EosBandi/OSDeluxe/params.cpp

/*
	OSDeluxe - Color PIP Mavlink OSD
	Copyright (C) 2018  Andras Schaffer - Dronedoktor.eu

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
	With Grateful Acknowledgements to the projects:
		AlceOSD by Luis Alves
		PlayUAV OSD
		Brain FPV Flight Controller(https://github.com/BrainFPV/TauLabs) by Tau Labs

 */

#include "osdeluxe.h"

#define PARAM(n, t, p, c) {  n, t, (void *) p,  c }
#define PARAM_END { "" }

int total_params;						// Number of all params (int, to eliminate warning about unsigned, signed comparisions
int param_send_index;

struct param_def parameters[] = {
	//Generic parameters

	PARAM("VIN1_SHARPENING", MAV_PARAM_TYPE_UINT8,&osd.vin_params[0].sharpening, &update_vin_settings),
	PARAM("VIN1_SATURATION", MAV_PARAM_TYPE_UINT8,&osd.vin_params[0].saturation, &update_vin_settings),
	PARAM("VIN1_CONTRAST",   MAV_PARAM_TYPE_UINT8,&osd.vin_params[0].contrast, &update_vin_settings),
	PARAM("VIN1_BRIGHTNESS", MAV_PARAM_TYPE_UINT8,&osd.vin_params[0].brightness, &update_vin_settings),
	PARAM("VIN1_ENHANCE",    MAV_PARAM_TYPE_UINT8,&osd.vin_params[0].enhance, &update_vin_settings),
	PARAM("VIN1_H_MIRROR",   MAV_PARAM_TYPE_UINT8,&osd.vin_params[0].h_mirror, &update_vin_settings),
	PARAM("VIN1_V_MIRROR",   MAV_PARAM_TYPE_UINT8,&osd.vin_params[0].v_mirror, &update_vin_settings),
	PARAM("VIN1_BOUNDARY",   MAV_PARAM_TYPE_UINT8,&osd.vin_params[0].boundary, &update_vin_settings),
	PARAM("VIN1_PEAKING",    MAV_PARAM_TYPE_UINT8,&osd.vin_params[0].peaking, &update_vin_settings),

	PARAM("VIN2_SHARPENING", MAV_PARAM_TYPE_UINT8,&osd.vin_params[1].sharpening, &update_vin_settings),
	PARAM("VIN2_SATURATION", MAV_PARAM_TYPE_UINT8,&osd.vin_params[1].saturation, &update_vin_settings),
	PARAM("VIN2_CONTRAST",   MAV_PARAM_TYPE_UINT8,&osd.vin_params[1].contrast, &update_vin_settings),
	PARAM("VIN2_BRIGHTNESS", MAV_PARAM_TYPE_UINT8,&osd.vin_params[1].brightness, &update_vin_settings),
	PARAM("VIN2_ENHANCE",    MAV_PARAM_TYPE_UINT8,&osd.vin_params[1].enhance, &update_vin_settings),
	PARAM("VIN2_H_MIRROR",   MAV_PARAM_TYPE_UINT8,&osd.vin_params[1].h_mirror, &update_vin_settings),
	PARAM("VIN2_V_MIRROR",   MAV_PARAM_TYPE_UINT8,&osd.vin_params[1].v_mirror, &update_vin_settings),
	PARAM("VIN2_BOUNDARY",   MAV_PARAM_TYPE_UINT8,&osd.vin_params[1].boundary, &update_vin_settings),
	PARAM("VIN2_PEAKING",    MAV_PARAM_TYPE_UINT8,&osd.vin_params[1].peaking, &update_vin_settings),

	PARAM("VIN3_SHARPENING", MAV_PARAM_TYPE_UINT8,&osd.vin_params[2].sharpening, &update_vin_settings),
	PARAM("VIN3_SATURATION", MAV_PARAM_TYPE_UINT8,&osd.vin_params[2].saturation, &update_vin_settings),
	PARAM("VIN3_CONTRAST",   MAV_PARAM_TYPE_UINT8,&osd.vin_params[2].contrast, &update_vin_settings),
	PARAM("VIN3_BRIGHTNESS", MAV_PARAM_TYPE_UINT8,&osd.vin_params[2].brightness, &update_vin_settings),
	PARAM("VIN3_ENHANCE",    MAV_PARAM_TYPE_UINT8,&osd.vin_params[2].enhance, &update_vin_settings),
	PARAM("VIN3_H_MIRROR",   MAV_PARAM_TYPE_UINT8,&osd.vin_params[2].h_mirror, &update_vin_settings),
	PARAM("VIN3_V_MIRROR",   MAV_PARAM_TYPE_UINT8,&osd.vin_params[2].v_mirror, &update_vin_settings),
	PARAM("VIN3_BOUNDARY",   MAV_PARAM_TYPE_UINT8,&osd.vin_params[2].boundary, &update_vin_settings),
	PARAM("VIN3_PEAKING",    MAV_PARAM_TYPE_UINT8,&osd.vin_params[2].peaking, &update_vin_settings),

	PARAM("VIN4_SHARPENING", MAV_PARAM_TYPE_UINT8,&osd.vin_params[3].sharpening, &update_vin_settings),
	PARAM("VIN4_SATURATION", MAV_PARAM_TYPE_UINT8,&osd.vin_params[3].saturation, &update_vin_settings),
	PARAM("VIN4_CONTRAST",   MAV_PARAM_TYPE_UINT8,&osd.vin_params[3].contrast, &update_vin_settings),
	PARAM("VIN4_BRIGHTNESS", MAV_PARAM_TYPE_UINT8,&osd.vin_params[3].brightness, &update_vin_settings),
	PARAM("VIN4_ENHANCE",    MAV_PARAM_TYPE_UINT8,&osd.vin_params[3].enhance, &update_vin_settings),
	PARAM("VIN4_H_MIRROR",   MAV_PARAM_TYPE_UINT8,&osd.vin_params[3].h_mirror, &update_vin_settings),
	PARAM("VIN4_V_MIRROR",   MAV_PARAM_TYPE_UINT8,&osd.vin_params[3].v_mirror, &update_vin_settings),
	PARAM("VIN4_BOUNDARY",   MAV_PARAM_TYPE_UINT8,&osd.vin_params[3].boundary, &update_vin_settings),
	PARAM("VIN4_PEAKING",    MAV_PARAM_TYPE_UINT8,&osd.vin_params[3].peaking, &update_vin_settings),


	PARAM("VARIO_POSX", MAV_PARAM_TYPE_UINT16, &osd.vario.x, NULL),
	PARAM("VARIO_POSY", MAV_PARAM_TYPE_UINT16, &osd.vario.y, NULL),
	PARAM("VARIO_HEIGHT", MAV_PARAM_TYPE_UINT16, &osd.vario.h, NULL),
	PARAM("VARIO_WIDTH", MAV_PARAM_TYPE_UINT16, &osd.vario.w, NULL),
	PARAM("VARIO_NUMPOS", MAV_PARAM_TYPE_UINT8, &osd.vario.num_pos, NULL),
	PARAM("VARIO_MAXIMUM", MAV_PARAM_TYPE_REAL32, &osd.vario.vario_max, NULL),

	PARAM("VGRAPH_POSX", MAV_PARAM_TYPE_UINT16, &osd.vgraph.x, &do_update_pthy),
	PARAM("VGRAPH_POSY", MAV_PARAM_TYPE_UINT16, &osd.vgraph.y, &do_update_pthy),
	PARAM("VGRAPH_HEIGHT", MAV_PARAM_TYPE_UINT16, &osd.vgraph.h, &do_update_pthy),
	PARAM("VGRAPH_MAXIMUM", MAV_PARAM_TYPE_REAL32, &osd.vgraph.vario_max, NULL),
	PARAM("VGRAPH_MIX", MAV_PARAM_TYPE_UINT8, &osd.vgraph.mix, NULL),


	PARAM("GPS_POSX", MAV_PARAM_TYPE_UINT16, &osd.gps.x, NULL),
	PARAM("GPS_POSY", MAV_PARAM_TYPE_UINT16, &osd.gps.y, NULL),
	PARAM("GPS_SAT_WARNING", MAV_PARAM_TYPE_UINT8, &osd.gps.sat_warn, NULL),
	PARAM("GPS_HDOP_WARNING", MAV_PARAM_TYPE_REAL32, &osd.gps.hdop_warn, NULL),
	PARAM("GPS_SAT_CRITICAL", MAV_PARAM_TYPE_UINT8, &osd.gps.sat_critical, NULL),
	PARAM("GPS_HDOP_CRITCAL", MAV_PARAM_TYPE_REAL32, &osd.gps.hdop_critical, NULL),

	PARAM("RSSI_POSX", MAV_PARAM_TYPE_UINT16, &osd.rssi.x, NULL),
	PARAM("RSSI_POSY", MAV_PARAM_TYPE_UINT16, &osd.rssi.y, NULL),
	PARAM("RSSI_WARNING", MAV_PARAM_TYPE_UINT8, &osd.rssi.rssi_warning, NULL),
	PARAM("RSSI_CRITICAL", MAV_PARAM_TYPE_UINT8, &osd.rssi.rssi_critical, NULL),


//     01234567890123456
	PARAM("BAT1V_POSX", MAV_PARAM_TYPE_UINT16, &osd.batt1_v.x, NULL),
	PARAM("BAT1V_POSY", MAV_PARAM_TYPE_UINT16, &osd.batt1_v.y, NULL),
	PARAM("BAT1V_CELLS", MAV_PARAM_TYPE_UINT8, &osd.batt1_v.cells, NULL),
	PARAM("BAT1V_MINCELLV", MAV_PARAM_TYPE_REAL32, &osd.batt1_v.min_cell_voltage, NULL),
	PARAM("BAT1V_MAXCELLV", MAV_PARAM_TYPE_REAL32, &osd.batt1_v.max_cell_voltage, NULL),
	PARAM("BAT1V_YELWCELLV", MAV_PARAM_TYPE_REAL32, &osd.batt1_v.yellow_cell_voltage, NULL),
	PARAM("BAT1V_REDCELLV", MAV_PARAM_TYPE_REAL32, &osd.batt1_v.red_cell_voltage, NULL),
	PARAM("BAT1V_BARTYPE", MAV_PARAM_TYPE_UINT8, &osd.batt1_v.bar_type, NULL),

	PARAM("BAT2V_POSX", MAV_PARAM_TYPE_UINT16, &osd.batt2_v.x, NULL),
	PARAM("BAT2V_POSY", MAV_PARAM_TYPE_UINT16, &osd.batt2_v.y, NULL),
	PARAM("BAT2V_CELLS", MAV_PARAM_TYPE_UINT8, &osd.batt2_v.cells, NULL),
	PARAM("BAT2V_MINCELLV", MAV_PARAM_TYPE_REAL32, &osd.batt2_v.min_cell_voltage, NULL),
	PARAM("BAT2V_MAXCELLV", MAV_PARAM_TYPE_REAL32, &osd.batt2_v.max_cell_voltage, NULL),
	PARAM("BAT2V_YELWCELLV", MAV_PARAM_TYPE_REAL32, &osd.batt2_v.yellow_cell_voltage, NULL),
	PARAM("BAT2V_REDCELLV", MAV_PARAM_TYPE_REAL32, &osd.batt2_v.red_cell_voltage, NULL),
	PARAM("BAT2V_BARTYPE", MAV_PARAM_TYPE_UINT8, &osd.batt2_v.bar_type, NULL),

	PARAM("BAT1CAP_POSX", MAV_PARAM_TYPE_UINT16, &osd.batt1_cap.x, NULL),
	PARAM("BAT1CAP_POSY", MAV_PARAM_TYPE_UINT16, &osd.batt1_cap.y, NULL),
	PARAM("BAT1CAP_BARTYPE", MAV_PARAM_TYPE_UINT8, &osd.batt1_cap.bar_type, NULL),

	PARAM("BAT1CUR_POSX", MAV_PARAM_TYPE_UINT16, &osd.batt1_curr.x, NULL),
	PARAM("BAT1CUR_POSY", MAV_PARAM_TYPE_UINT16, &osd.batt1_curr.y, NULL),

	PARAM("BAT2CUR_POSX", MAV_PARAM_TYPE_UINT16, &osd.batt2_curr.x, NULL),
	PARAM("BAT2CUR_POSY", MAV_PARAM_TYPE_UINT16, &osd.batt2_curr.y, NULL),

	PARAM("BAT1PWR_POSX", MAV_PARAM_TYPE_UINT16, &osd.batt1_power.x, NULL),
	PARAM("BAT1PWR_POSY", MAV_PARAM_TYPE_UINT16, &osd.batt1_power.y, NULL),

	PARAM("BAT2PWR_POSX", MAV_PARAM_TYPE_UINT16, &osd.batt2_power.x, NULL),
	PARAM("BAT2PWR_POSY", MAV_PARAM_TYPE_UINT16, &osd.batt2_power.y, NULL),

	PARAM("STATUS_POSX", MAV_PARAM_TYPE_UINT16, &osd.stat.x, NULL),
	PARAM("STATUS_POSY", MAV_PARAM_TYPE_UINT16, &osd.stat.y, NULL),

	PARAM("ALT_POSX", MAV_PARAM_TYPE_UINT16, &osd.alt.x, NULL),
	PARAM("ALT_POSY", MAV_PARAM_TYPE_UINT16, &osd.alt.y, NULL),

	PARAM("COMPASS_POSX", MAV_PARAM_TYPE_UINT16, &osd.compass.x, NULL),
	PARAM("COMPASS_POSY", MAV_PARAM_TYPE_UINT16, &osd.compass.y, NULL),

	PARAM("PULL_POSX", MAV_PARAM_TYPE_UINT16, &osd.pull.x, NULL),
	PARAM("PULL_POSY", MAV_PARAM_TYPE_UINT16, &osd.pull.y, NULL),
	PARAM("PULL_WARNING", MAV_PARAM_TYPE_REAL32, &osd.pull.warning, NULL),

	PARAM("HOME_POSX", MAV_PARAM_TYPE_UINT16, &osd.home_w.x, NULL),
	PARAM("HOME_POSY", MAV_PARAM_TYPE_UINT16, &osd.home_w.y, NULL),

	PARAM("MODE_POSX", MAV_PARAM_TYPE_UINT16, &osd.mode.mode_x, NULL),
	PARAM("MODE_POSY", MAV_PARAM_TYPE_UINT16, &osd.mode.mode_y, NULL),
	PARAM("MODE_CENTERED", MAV_PARAM_TYPE_UINT8, &osd.mode.mode_centered, NULL),
	PARAM("MODE_SHORT", MAV_PARAM_TYPE_UINT8, &osd.mode.mode_short, NULL),

	PARAM("FAILSAFE_POSX", MAV_PARAM_TYPE_UINT16, &osd.mode.fs_x, NULL),
	PARAM("FAILSAFE_POSY", MAV_PARAM_TYPE_UINT16, &osd.mode.fs_y, NULL),
	PARAM("FAILSAFE_CENTERD", MAV_PARAM_TYPE_UINT8, &osd.mode.fs_centered, NULL),

	PARAM("ARM_POSX", MAV_PARAM_TYPE_UINT16, &osd.mode.arm_x, NULL),
	PARAM("ARM_POSY", MAV_PARAM_TYPE_UINT16, &osd.mode.arm_y, NULL),
	PARAM("ARM_CENTERD", MAV_PARAM_TYPE_UINT8, &osd.mode.arm_centered, NULL),

	PARAM("MESSAGE_POSX", MAV_PARAM_TYPE_UINT16, &osd.msg_widget.x, NULL),
	PARAM("MESSAGE_POSY", MAV_PARAM_TYPE_UINT16, &osd.msg_widget.y, NULL),

	PARAM("MSG_LIST_POSX", MAV_PARAM_TYPE_UINT16, &osd.msg_list_widget.x, NULL), 
	PARAM("MSG_LIST_POSY", MAV_PARAM_TYPE_UINT16, &osd.msg_list_widget.y, NULL),


	PARAM("GS_POSX", MAV_PARAM_TYPE_UINT16, &osd.gs.x, NULL),
	PARAM("GS_POSY", MAV_PARAM_TYPE_UINT16, &osd.gs.y, NULL),

	PARAM("THROTTLE_POSX", MAV_PARAM_TYPE_UINT16, &osd.thr.x, NULL),
	PARAM("THROTTLE_POSY", MAV_PARAM_TYPE_UINT16, &osd.thr.y, NULL),

	PARAM("MOVE_POSX", MAV_PARAM_TYPE_UINT16, &osd.move.x, &do_update_pthy),
	PARAM("MOVE_POSY", MAV_PARAM_TYPE_UINT16, &osd.move.y, &do_update_pthy),
	PARAM("MOVE_SIZE", MAV_PARAM_TYPE_UINT16, &osd.move.size, &do_update_pthy),
	PARAM("MOVE_MAX",  MAV_PARAM_TYPE_REAL32, &osd.move.max, NULL),

	PARAM("RADAR1_POSX", MAV_PARAM_TYPE_UINT16, &osd.radar1.x, &do_update_pthy),
	PARAM("RADAR1_POSY", MAV_PARAM_TYPE_UINT16, &osd.radar1.y, &do_update_pthy),
	PARAM("RADAR1_SIZE", MAV_PARAM_TYPE_UINT16, &osd.radar1.size, &do_update_pthy),
	PARAM("RADAR1_SCALE", MAV_PARAM_TYPE_UINT8, &osd.radar1.scale, &do_update_pthy),
	PARAM("RADAR1_TYPE", MAV_PARAM_TYPE_UINT8, &osd.radar1.type, &do_update_pthy),

	PARAM("RADAR2_POSX", MAV_PARAM_TYPE_UINT16, &osd.radar2.x, &do_update_pthy),
	PARAM("RADAR2_POSY", MAV_PARAM_TYPE_UINT16, &osd.radar2.y, &do_update_pthy),
	PARAM("RADAR2_SIZE", MAV_PARAM_TYPE_UINT16, &osd.radar2.size, &do_update_pthy),
	PARAM("RADAR2_SCALE", MAV_PARAM_TYPE_UINT8, &osd.radar2.scale, &do_update_pthy),
	PARAM("RADAR2_TYPE", MAV_PARAM_TYPE_UINT8, &osd.radar2.type, &do_update_pthy),

	PARAM("RADAR3_POSX", MAV_PARAM_TYPE_UINT16, &osd.radar3.x, &do_update_pthy),
	PARAM("RADAR3_POSY", MAV_PARAM_TYPE_UINT16, &osd.radar3.y, &do_update_pthy),
	PARAM("RADAR3_SIZE", MAV_PARAM_TYPE_UINT16, &osd.radar3.size, &do_update_pthy),
	PARAM("RADAR3_SCALE", MAV_PARAM_TYPE_UINT8, &osd.radar3.scale, &do_update_pthy),
	PARAM("RADAR3_TYPE", MAV_PARAM_TYPE_UINT8, &osd.radar3.type, &do_update_pthy),

	PARAM("CTR_RC_CH_1", MAV_PARAM_TYPE_UINT8, &osd.ctr_ch[0], NULL),
	PARAM("CTR_RC_CH_2", MAV_PARAM_TYPE_UINT8, &osd.ctr_ch[1], NULL),
	PARAM("CTR_RC_CH_3", MAV_PARAM_TYPE_UINT8, &osd.ctr_ch[2], NULL),
	PARAM("CTR_RC_CH_4", MAV_PARAM_TYPE_UINT8, &osd.ctr_ch[3], NULL),

	//bit coded field for osd widget visibility by pages (1-8 pages)
	PARAM("PAGE_GPS", MAV_PARAM_TYPE_UINT8, &osd.gps.visible, NULL),
	PARAM("PAGE_BATT1_VOLT", MAV_PARAM_TYPE_UINT8, &osd.batt1_v.visible, NULL),
	PARAM("PAGE_BATT2_VOLT", MAV_PARAM_TYPE_UINT8, &osd.batt2_v.visible, NULL),
	PARAM("PAGE_BATT1_CURR", MAV_PARAM_TYPE_UINT8, &osd.batt1_curr.visible, NULL),
	PARAM("PAGE_BATT2_CURR", MAV_PARAM_TYPE_UINT8, &osd.batt2_curr.visible, NULL),
	PARAM("PAGE_BATT1_CAP", MAV_PARAM_TYPE_UINT8, &osd.batt1_cap.visible, NULL),
	PARAM("PAGE_BATT1_PWR", MAV_PARAM_TYPE_UINT8, &osd.batt1_power.visible, NULL),
	PARAM("PAGE_BATT2_PWR", MAV_PARAM_TYPE_UINT8, &osd.batt2_power.visible, NULL),

	PARAM("PAGE_STAT", MAV_PARAM_TYPE_UINT8, &osd.stat.visible, NULL),
	PARAM("PAGE_ALT", MAV_PARAM_TYPE_UINT8, &osd.alt.visible, NULL),
	PARAM("PAGE_COMPASS", MAV_PARAM_TYPE_UINT8, &osd.compass.visible, NULL),
	PARAM("PAGE_VARIO", MAV_PARAM_TYPE_UINT8, &osd.vario.visible, NULL),
	PARAM("PAGE_HOME", MAV_PARAM_TYPE_UINT8, &osd.home_w.visible, NULL),
	PARAM("PAGE_HORIZON", MAV_PARAM_TYPE_UINT8, &osd.horizon.visible, NULL),
	PARAM("PAGE_MODE", MAV_PARAM_TYPE_UINT8, &osd.mode.visible, NULL),
	PARAM("PAGE_PULL", MAV_PARAM_TYPE_UINT8, &osd.pull.visible, NULL),
	PARAM("PAGE_MESSAGE", MAV_PARAM_TYPE_UINT8, &osd.msg_widget.visible, NULL),
	PARAM("PAGE_GS", MAV_PARAM_TYPE_UINT8, &osd.gs.visible, NULL),
	PARAM("PAGE_THROTTLE", MAV_PARAM_TYPE_UINT8, &osd.thr.visible, NULL),
    PARAM("PAGE_MOVE", MAV_PARAM_TYPE_UINT8, &osd.move.visible, NULL), 
	PARAM("PAGE_PT", MAV_PARAM_TYPE_UINT8, &osd.pt_widget.visible, NULL),
	PARAM("PAGE_CENTER_M", MAV_PARAM_TYPE_UINT8, &osd.center_cross_visible , &do_update_pthy),
	PARAM("PAGE_RADAR1", MAV_PARAM_TYPE_UINT8, &osd.radar1.visible, &do_update_pthy),
	PARAM("PAGE_RADAR2", MAV_PARAM_TYPE_UINT8, &osd.radar2.visible, &do_update_pthy),
	PARAM("PAGE_RADAR3", MAV_PARAM_TYPE_UINT8, &osd.radar3.visible, &do_update_pthy),
    PARAM("PAGE_RSSI",MAV_PARAM_TYPE_UINT8, &osd.rssi.visible, &do_update_pthy),
	PARAM("PAGE_EKF", MAV_PARAM_TYPE_UINT8, &osd.ekf_detail.visible, NULL), 
	PARAM("PAGE_VIBE", MAV_PARAM_TYPE_UINT8, &osd.vibe_detail.visible, NULL),
	PARAM("PAGE_MSG_LIST", MAV_PARAM_TYPE_UINT8, &osd.msg_list_widget.visible, NULL), 
	PARAM("PAGE_RCOUT", MAV_PARAM_TYPE_UINT8, &osd.rc_out.visible, NULL),


		
	PARAM("PAGE_BOX_1", MAV_PARAM_TYPE_INT16, &osd.boxes[0].visible, &do_update_pthy),
	PARAM("PAGE_BOX_2", MAV_PARAM_TYPE_INT16, &osd.boxes[1].visible, &do_update_pthy),
	PARAM("PAGE_BOX_3", MAV_PARAM_TYPE_INT16, &osd.boxes[2].visible, &do_update_pthy),
	PARAM("PAGE_BOX_4", MAV_PARAM_TYPE_INT16, &osd.boxes[3].visible, &do_update_pthy),
	PARAM("PAGE_BOX_5", MAV_PARAM_TYPE_INT16, &osd.boxes[4].visible, &do_update_pthy),
	PARAM("PAGE_BOX_6", MAV_PARAM_TYPE_INT16, &osd.boxes[5].visible, &do_update_pthy),
	PARAM("PAGE_BOX_7", MAV_PARAM_TYPE_INT16, &osd.boxes[6].visible, &do_update_pthy),
	PARAM("PAGE_BOX_8", MAV_PARAM_TYPE_INT16, &osd.boxes[7].visible, &do_update_pthy),

	PARAM("VOUT_COLOR_BAR", MAV_PARAM_TYPE_UINT8, &osd.color_bar_x, &update_vout_settings),
	PARAM("VOUT_COLOR_KILL", MAV_PARAM_TYPE_UINT8, &osd.color_kill_x, &update_vout_settings),
	PARAM("VOUT_OUT1_GAIN", MAV_PARAM_TYPE_UINT8, &osd.vout1_gain, &update_vout_settings),
	PARAM("VOUT_OUT2_GAIN", MAV_PARAM_TYPE_UINT8, &osd.vout2_gain, &update_vout_settings),
	PARAM("VOUT_OUT3_GAIN", MAV_PARAM_TYPE_UINT8, &osd.vout3_gain, &update_vout_settings),


	PARAM("PIPM0_POS_H_CH1", MAV_PARAM_TYPE_UINT8, &osd.video_channels[0][1].pos_h, &update_pip),
	PARAM("PIPM0_POS_V_CH1", MAV_PARAM_TYPE_UINT8, &osd.video_channels[0][1].pos_v, &update_pip),
	PARAM("PIPM0_SIZE_CH1",  MAV_PARAM_TYPE_UINT8, &osd.video_channels[0][1].len_h, &update_pip),
	PARAM("PIPM0_INPUT_CH1", MAV_PARAM_TYPE_UINT8, &osd.video_channels[0][1].input, &update_pip),
	PARAM("PIPM0_POPUP_CH1", MAV_PARAM_TYPE_UINT8, &osd.video_channels[0][1].popup, &update_pip),
	PARAM("PIPM0_ENA_CH1",   MAV_PARAM_TYPE_UINT8, &osd.video_channels[0][1].enable, &update_pip),

	PARAM("PIPM0_POS_H_CH2", MAV_PARAM_TYPE_UINT8, &osd.video_channels[0][2].pos_h, &update_pip),
	PARAM("PIPM0_POS_V_CH2", MAV_PARAM_TYPE_UINT8, &osd.video_channels[0][2].pos_v, &update_pip),
	PARAM("PIPM0_SIZE_CH2",  MAV_PARAM_TYPE_UINT8, &osd.video_channels[0][2].len_h, &update_pip),
	PARAM("PIPM0_INPUT_CH2", MAV_PARAM_TYPE_UINT8, &osd.video_channels[0][2].input, &update_pip),
	PARAM("PIPM0_POPUP_CH2", MAV_PARAM_TYPE_UINT8, &osd.video_channels[0][2].popup, &update_pip),
	PARAM("PIPM0_ENA_CH2",   MAV_PARAM_TYPE_UINT8, &osd.video_channels[0][2].enable, &update_pip),

	PARAM("PIPM0_POS_H_CH3", MAV_PARAM_TYPE_UINT8, &osd.video_channels[0][3].pos_h, &update_pip),
	PARAM("PIPM0_POS_V_CH3", MAV_PARAM_TYPE_UINT8, &osd.video_channels[0][3].pos_v, &update_pip),
	PARAM("PIPM0_SIZE_CH3",  MAV_PARAM_TYPE_UINT8, &osd.video_channels[0][3].len_h, &update_pip),
	PARAM("PIPM0_INPUT_CH3", MAV_PARAM_TYPE_UINT8, &osd.video_channels[0][3].input, &update_pip),
	PARAM("PIPM0_POPUP_CH3", MAV_PARAM_TYPE_UINT8, &osd.video_channels[0][3].popup, &update_pip),
	PARAM("PIPM0_ENA_CH3",   MAV_PARAM_TYPE_UINT8, &osd.video_channels[0][3].enable, &update_pip),

	PARAM("PIPM0_POS_H_CH4", MAV_PARAM_TYPE_UINT8, &osd.video_channels[0][4].pos_h, &update_pip),
	PARAM("PIPM0_POS_V_CH4", MAV_PARAM_TYPE_UINT8, &osd.video_channels[0][4].pos_v, &update_pip),
	PARAM("PIPM0_SIZE_CH4",  MAV_PARAM_TYPE_UINT8, &osd.video_channels[0][4].len_h, &update_pip),
	PARAM("PIPM0_INPUT_CH4", MAV_PARAM_TYPE_UINT8, &osd.video_channels[0][4].input, &update_pip),
	PARAM("PIPM0_POPUP_CH4", MAV_PARAM_TYPE_UINT8, &osd.video_channels[0][4].popup, &update_pip),
	PARAM("PIPM0_ENA_CH4",   MAV_PARAM_TYPE_UINT8, &osd.video_channels[0][4].enable, &update_pip),

	PARAM("PIPM1_POS_H_CH1", MAV_PARAM_TYPE_UINT8, &osd.video_channels[1][1].pos_h, &update_pip),
	PARAM("PIPM1_POS_V_CH1", MAV_PARAM_TYPE_UINT8, &osd.video_channels[1][1].pos_v, &update_pip),
	PARAM("PIPM1_SIZE_CH1",  MAV_PARAM_TYPE_UINT8, &osd.video_channels[1][1].len_h, &update_pip),
	PARAM("PIPM1_INPUT_CH1", MAV_PARAM_TYPE_UINT8, &osd.video_channels[1][1].input, &update_pip),
	PARAM("PIPM1_POPUP_CH1", MAV_PARAM_TYPE_UINT8, &osd.video_channels[1][1].popup, &update_pip),
	PARAM("PIPM1_ENA_CH1",   MAV_PARAM_TYPE_UINT8, &osd.video_channels[1][1].enable, &update_pip),

	PARAM("PIPM1_POS_H_CH2", MAV_PARAM_TYPE_UINT8, &osd.video_channels[1][2].pos_h, &update_pip),
	PARAM("PIPM1_POS_V_CH2", MAV_PARAM_TYPE_UINT8, &osd.video_channels[1][2].pos_v, &update_pip),
	PARAM("PIPM1_SIZE_CH2",  MAV_PARAM_TYPE_UINT8, &osd.video_channels[1][2].len_h, &update_pip),
	PARAM("PIPM1_INPUT_CH2", MAV_PARAM_TYPE_UINT8, &osd.video_channels[1][2].input, &update_pip),
	PARAM("PIPM1_POPUP_CH2", MAV_PARAM_TYPE_UINT8, &osd.video_channels[1][2].popup, &update_pip),
	PARAM("PIPM1_ENA_CH2",   MAV_PARAM_TYPE_UINT8, &osd.video_channels[1][2].enable, &update_pip),

	PARAM("PIPM1_POS_H_CH3", MAV_PARAM_TYPE_UINT8, &osd.video_channels[1][3].pos_h, &update_pip),
	PARAM("PIPM1_POS_V_CH3", MAV_PARAM_TYPE_UINT8, &osd.video_channels[1][3].pos_v, &update_pip),
	PARAM("PIPM1_SIZE_CH3",  MAV_PARAM_TYPE_UINT8, &osd.video_channels[1][3].len_h, &update_pip),
	PARAM("PIPM1_INPUT_CH3", MAV_PARAM_TYPE_UINT8, &osd.video_channels[1][3].input, &update_pip),
	PARAM("PIPM1_POPUP_CH3", MAV_PARAM_TYPE_UINT8, &osd.video_channels[1][3].popup, &update_pip),
	PARAM("PIPM1_ENA_CH3",   MAV_PARAM_TYPE_UINT8, &osd.video_channels[1][3].enable, &update_pip),

	PARAM("PIPM1_POS_H_CH4", MAV_PARAM_TYPE_UINT8, &osd.video_channels[1][4].pos_h, &update_pip),
	PARAM("PIPM1_POS_V_CH4", MAV_PARAM_TYPE_UINT8, &osd.video_channels[1][4].pos_v, &update_pip),
	PARAM("PIPM1_SIZE_CH4",  MAV_PARAM_TYPE_UINT8, &osd.video_channels[1][4].len_h, &update_pip),
	PARAM("PIPM1_INPUT_CH4", MAV_PARAM_TYPE_UINT8, &osd.video_channels[1][4].input, &update_pip),
	PARAM("PIPM1_POPUP_CH4", MAV_PARAM_TYPE_UINT8, &osd.video_channels[1][4].popup, &update_pip),
	PARAM("PIPM1_ENA_CH4",   MAV_PARAM_TYPE_UINT8, &osd.video_channels[1][4].enable, &update_pip),
//---
	PARAM("PIPM2_POS_H_CH1", MAV_PARAM_TYPE_UINT8, &osd.video_channels[2][1].pos_h, &update_pip),
	PARAM("PIPM2_POS_V_CH1", MAV_PARAM_TYPE_UINT8, &osd.video_channels[2][1].pos_v, &update_pip),
	PARAM("PIPM2_SIZE_CH1",  MAV_PARAM_TYPE_UINT8, &osd.video_channels[2][1].len_h, &update_pip),
	PARAM("PIPM2_INPUT_CH1", MAV_PARAM_TYPE_UINT8, &osd.video_channels[2][1].input, &update_pip),
	PARAM("PIPM2_POPUP_CH1", MAV_PARAM_TYPE_UINT8, &osd.video_channels[2][1].popup, &update_pip),
	PARAM("PIPM2_ENA_CH1",   MAV_PARAM_TYPE_UINT8, &osd.video_channels[2][1].enable, &update_pip),

	PARAM("PIPM2_POS_H_CH2", MAV_PARAM_TYPE_UINT8, &osd.video_channels[2][2].pos_h, &update_pip),
	PARAM("PIPM2_POS_V_CH2", MAV_PARAM_TYPE_UINT8, &osd.video_channels[2][2].pos_v, &update_pip),
	PARAM("PIPM2_SIZE_CH2",  MAV_PARAM_TYPE_UINT8, &osd.video_channels[2][2].len_h, &update_pip),
	PARAM("PIPM2_INPUT_CH2", MAV_PARAM_TYPE_UINT8, &osd.video_channels[2][2].input, &update_pip),
	PARAM("PIPM2_POPUP_CH2", MAV_PARAM_TYPE_UINT8, &osd.video_channels[2][2].popup, &update_pip),
	PARAM("PIPM2_ENA_CH2",   MAV_PARAM_TYPE_UINT8, &osd.video_channels[2][2].enable, &update_pip),

	PARAM("PIPM2_POS_H_CH3", MAV_PARAM_TYPE_UINT8, &osd.video_channels[2][3].pos_h, &update_pip),
	PARAM("PIPM2_POS_V_CH3", MAV_PARAM_TYPE_UINT8, &osd.video_channels[2][3].pos_v, &update_pip),
	PARAM("PIPM2_SIZE_CH3",  MAV_PARAM_TYPE_UINT8, &osd.video_channels[2][3].len_h, &update_pip),
	PARAM("PIPM2_INPUT_CH3", MAV_PARAM_TYPE_UINT8, &osd.video_channels[2][3].input, &update_pip),
	PARAM("PIPM2_POPUP_CH3", MAV_PARAM_TYPE_UINT8, &osd.video_channels[2][3].popup, &update_pip),
	PARAM("PIPM2_ENA_CH3",   MAV_PARAM_TYPE_UINT8, &osd.video_channels[2][3].enable, &update_pip),

	PARAM("PIPM2_POS_H_CH4", MAV_PARAM_TYPE_UINT8, &osd.video_channels[2][4].pos_h, &update_pip),
	PARAM("PIPM2_POS_V_CH4", MAV_PARAM_TYPE_UINT8, &osd.video_channels[2][4].pos_v, &update_pip),
	PARAM("PIPM2_SIZE_CH4",  MAV_PARAM_TYPE_UINT8, &osd.video_channels[2][4].len_h, &update_pip),
	PARAM("PIPM2_INPUT_CH4", MAV_PARAM_TYPE_UINT8, &osd.video_channels[2][4].input, &update_pip),
	PARAM("PIPM2_POPUP_CH4", MAV_PARAM_TYPE_UINT8, &osd.video_channels[2][4].popup, &update_pip),
	PARAM("PIPM2_ENA_CH4",   MAV_PARAM_TYPE_UINT8, &osd.video_channels[2][4].enable, &update_pip),
//---
	PARAM("PIPM3_POS_H_CH1", MAV_PARAM_TYPE_UINT8, &osd.video_channels[3][1].pos_h, &update_pip),
	PARAM("PIPM3_POS_V_CH1", MAV_PARAM_TYPE_UINT8, &osd.video_channels[3][1].pos_v, &update_pip),
	PARAM("PIPM3_SIZE_CH1",  MAV_PARAM_TYPE_UINT8, &osd.video_channels[3][1].len_h, &update_pip),
	PARAM("PIPM3_INPUT_CH1", MAV_PARAM_TYPE_UINT8, &osd.video_channels[3][1].input, &update_pip),
	PARAM("PIPM3_POPUP_CH1", MAV_PARAM_TYPE_UINT8, &osd.video_channels[3][1].popup, &update_pip),
	PARAM("PIPM3_ENA_CH1",   MAV_PARAM_TYPE_UINT8, &osd.video_channels[3][1].enable, &update_pip),

	PARAM("PIPM3_POS_H_CH2", MAV_PARAM_TYPE_UINT8, &osd.video_channels[3][2].pos_h, &update_pip),
	PARAM("PIPM3_POS_V_CH2", MAV_PARAM_TYPE_UINT8, &osd.video_channels[3][2].pos_v, &update_pip),
	PARAM("PIPM3_SIZE_CH2",  MAV_PARAM_TYPE_UINT8, &osd.video_channels[3][2].len_h, &update_pip),
	PARAM("PIPM3_INPUT_CH2", MAV_PARAM_TYPE_UINT8, &osd.video_channels[3][2].input, &update_pip),
	PARAM("PIPM3_POPUP_CH2", MAV_PARAM_TYPE_UINT8, &osd.video_channels[3][2].popup, &update_pip),
	PARAM("PIPM3_ENA_CH2",   MAV_PARAM_TYPE_UINT8, &osd.video_channels[3][2].enable, &update_pip),

	PARAM("PIPM3_POS_H_CH3", MAV_PARAM_TYPE_UINT8, &osd.video_channels[3][3].pos_h, &update_pip),
	PARAM("PIPM3_POS_V_CH3", MAV_PARAM_TYPE_UINT8, &osd.video_channels[3][3].pos_v, &update_pip),
	PARAM("PIPM3_SIZE_CH3",  MAV_PARAM_TYPE_UINT8, &osd.video_channels[3][3].len_h, &update_pip),
	PARAM("PIPM3_INPUT_CH3", MAV_PARAM_TYPE_UINT8, &osd.video_channels[3][3].input, &update_pip),
	PARAM("PIPM3_POPUP_CH3", MAV_PARAM_TYPE_UINT8, &osd.video_channels[3][3].popup, &update_pip),
	PARAM("PIPM3_ENA_CH3",   MAV_PARAM_TYPE_UINT8, &osd.video_channels[3][3].enable, &update_pip),

	PARAM("PIPM3_POS_H_CH4", MAV_PARAM_TYPE_UINT8, &osd.video_channels[3][4].pos_h, &update_pip),
	PARAM("PIPM3_POS_V_CH4", MAV_PARAM_TYPE_UINT8, &osd.video_channels[3][4].pos_v, &update_pip),
	PARAM("PIPM3_SIZE_CH4",  MAV_PARAM_TYPE_UINT8, &osd.video_channels[3][4].len_h, &update_pip),
	PARAM("PIPM3_INPUT_CH4", MAV_PARAM_TYPE_UINT8, &osd.video_channels[3][4].input, &update_pip),
	PARAM("PIPM3_POPUP_CH4", MAV_PARAM_TYPE_UINT8, &osd.video_channels[3][4].popup, &update_pip),
	PARAM("PIPM3_ENA_CH4",   MAV_PARAM_TYPE_UINT8, &osd.video_channels[3][4].enable, &update_pip),
//-----
	PARAM("PIPM4_POS_H_CH1", MAV_PARAM_TYPE_UINT8, &osd.video_channels[4][1].pos_h, &update_pip),
	PARAM("PIPM4_POS_V_CH1", MAV_PARAM_TYPE_UINT8, &osd.video_channels[4][1].pos_v, &update_pip),
	PARAM("PIPM4_SIZE_CH1",  MAV_PARAM_TYPE_UINT8, &osd.video_channels[4][1].len_h, &update_pip),
	PARAM("PIPM4_INPUT_CH1", MAV_PARAM_TYPE_UINT8, &osd.video_channels[4][1].input, &update_pip),
	PARAM("PIPM4_POPUP_CH1", MAV_PARAM_TYPE_UINT8, &osd.video_channels[4][1].popup, &update_pip),
	PARAM("PIPM4_ENA_CH1",   MAV_PARAM_TYPE_UINT8, &osd.video_channels[4][1].enable, &update_pip),

	PARAM("PIPM4_POS_H_CH2", MAV_PARAM_TYPE_UINT8, &osd.video_channels[4][2].pos_h, &update_pip),
	PARAM("PIPM4_POS_V_CH2", MAV_PARAM_TYPE_UINT8, &osd.video_channels[4][2].pos_v, &update_pip),
	PARAM("PIPM4_SIZE_CH2",  MAV_PARAM_TYPE_UINT8, &osd.video_channels[4][2].len_h, &update_pip),
	PARAM("PIPM4_INPUT_CH2", MAV_PARAM_TYPE_UINT8, &osd.video_channels[4][2].input, &update_pip),
	PARAM("PIPM4_POPUP_CH2", MAV_PARAM_TYPE_UINT8, &osd.video_channels[4][2].popup, &update_pip),
	PARAM("PIPM4_ENA_CH2",   MAV_PARAM_TYPE_UINT8, &osd.video_channels[4][2].enable, &update_pip),

	PARAM("PIPM4_POS_H_CH3", MAV_PARAM_TYPE_UINT8, &osd.video_channels[4][3].pos_h, &update_pip),
	PARAM("PIPM4_POS_V_CH3", MAV_PARAM_TYPE_UINT8, &osd.video_channels[4][3].pos_v, &update_pip),
	PARAM("PIPM4_SIZE_CH3",  MAV_PARAM_TYPE_UINT8, &osd.video_channels[4][3].len_h, &update_pip),
	PARAM("PIPM4_INPUT_CH3", MAV_PARAM_TYPE_UINT8, &osd.video_channels[4][3].input, &update_pip),
	PARAM("PIPM4_POPUP_CH3", MAV_PARAM_TYPE_UINT8, &osd.video_channels[4][3].popup, &update_pip),
	PARAM("PIPM4_ENA_CH3",   MAV_PARAM_TYPE_UINT8, &osd.video_channels[4][3].enable, &update_pip),

	PARAM("PIPM4_POS_H_CH4", MAV_PARAM_TYPE_UINT8, &osd.video_channels[4][4].pos_h, &update_pip),
	PARAM("PIPM4_POS_V_CH4", MAV_PARAM_TYPE_UINT8, &osd.video_channels[4][4].pos_v, &update_pip),
	PARAM("PIPM4_SIZE_CH4",  MAV_PARAM_TYPE_UINT8, &osd.video_channels[4][4].len_h, &update_pip),
	PARAM("PIPM4_INPUT_CH4", MAV_PARAM_TYPE_UINT8, &osd.video_channels[4][4].input, &update_pip),
	PARAM("PIPM4_POPUP_CH4", MAV_PARAM_TYPE_UINT8, &osd.video_channels[4][4].popup, &update_pip),
	PARAM("PIPM4_ENA_CH4",   MAV_PARAM_TYPE_UINT8, &osd.video_channels[4][4].enable, &update_pip),
//-----
	PARAM("PIPM5_POS_H_CH1", MAV_PARAM_TYPE_UINT8, &osd.video_channels[5][1].pos_h, &update_pip),
	PARAM("PIPM5_POS_V_CH1", MAV_PARAM_TYPE_UINT8, &osd.video_channels[5][1].pos_v, &update_pip),
	PARAM("PIPM5_SIZE_CH1",  MAV_PARAM_TYPE_UINT8, &osd.video_channels[5][1].len_h, &update_pip),
	PARAM("PIPM5_INPUT_CH1", MAV_PARAM_TYPE_UINT8, &osd.video_channels[5][1].input, &update_pip),
	PARAM("PIPM5_POPUP_CH1", MAV_PARAM_TYPE_UINT8, &osd.video_channels[5][1].popup, &update_pip),
	PARAM("PIPM5_ENA_CH1",   MAV_PARAM_TYPE_UINT8, &osd.video_channels[5][1].enable, &update_pip),

	PARAM("PIPM5_POS_H_CH2", MAV_PARAM_TYPE_UINT8, &osd.video_channels[5][2].pos_h, &update_pip),
	PARAM("PIPM5_POS_V_CH2", MAV_PARAM_TYPE_UINT8, &osd.video_channels[5][2].pos_v, &update_pip),
	PARAM("PIPM5_SIZE_CH2",  MAV_PARAM_TYPE_UINT8, &osd.video_channels[5][2].len_h, &update_pip),
	PARAM("PIPM5_INPUT_CH2", MAV_PARAM_TYPE_UINT8, &osd.video_channels[5][2].input, &update_pip),
	PARAM("PIPM5_POPUP_CH2", MAV_PARAM_TYPE_UINT8, &osd.video_channels[5][2].popup, &update_pip),
	PARAM("PIPM5_ENA_CH2",   MAV_PARAM_TYPE_UINT8, &osd.video_channels[5][2].enable, &update_pip),

	PARAM("PIPM5_POS_H_CH3", MAV_PARAM_TYPE_UINT8, &osd.video_channels[5][3].pos_h, &update_pip),
	PARAM("PIPM5_POS_V_CH3", MAV_PARAM_TYPE_UINT8, &osd.video_channels[5][3].pos_v, &update_pip),
	PARAM("PIPM5_SIZE_CH3",  MAV_PARAM_TYPE_UINT8, &osd.video_channels[5][3].len_h, &update_pip),
	PARAM("PIPM5_INPUT_CH3", MAV_PARAM_TYPE_UINT8, &osd.video_channels[5][3].input, &update_pip),
	PARAM("PIPM5_POPUP_CH3", MAV_PARAM_TYPE_UINT8, &osd.video_channels[5][3].popup, &update_pip),
	PARAM("PIPM5_ENA_CH3",   MAV_PARAM_TYPE_UINT8, &osd.video_channels[5][3].enable, &update_pip),

	PARAM("PIPM5_POS_H_CH4", MAV_PARAM_TYPE_UINT8, &osd.video_channels[5][4].pos_h, &update_pip),
	PARAM("PIPM5_POS_V_CH4", MAV_PARAM_TYPE_UINT8, &osd.video_channels[5][4].pos_v, &update_pip),
	PARAM("PIPM5_SIZE_CH4",  MAV_PARAM_TYPE_UINT8, &osd.video_channels[5][4].len_h, &update_pip),
	PARAM("PIPM5_INPUT_CH4", MAV_PARAM_TYPE_UINT8, &osd.video_channels[5][4].input, &update_pip),
	PARAM("PIPM5_POPUP_CH4", MAV_PARAM_TYPE_UINT8, &osd.video_channels[5][4].popup, &update_pip),
	PARAM("PIPM5_ENA_CH4",   MAV_PARAM_TYPE_UINT8, &osd.video_channels[5][4].enable, &update_pip),



	PARAM("BOX_1_X",	MAV_PARAM_TYPE_INT16,	&osd.boxes[0].x, &do_update_pthy),
	PARAM("BOX_1_Y",	MAV_PARAM_TYPE_INT16,	&osd.boxes[0].y, &do_update_pthy),
	PARAM("BOX_1_WIDTH",MAV_PARAM_TYPE_INT16,	&osd.boxes[0].w, &do_update_pthy),
	PARAM("BOX_1_HEIGHT",MAV_PARAM_TYPE_INT16,	&osd.boxes[0].h, &do_update_pthy),
	PARAM("BOX_1_COLOR", MAV_PARAM_TYPE_INT8,	&osd.boxes[0].color, &do_update_pthy),
	PARAM("BOX_1_MIX",	MAV_PARAM_TYPE_INT8,	&osd.boxes[0].mix, &do_update_pthy),

	PARAM("BOX_2_X", MAV_PARAM_TYPE_INT16, &osd.boxes[1].x, &do_update_pthy),
	PARAM("BOX_2_Y", MAV_PARAM_TYPE_INT16, &osd.boxes[1].y, &do_update_pthy),
	PARAM("BOX_2_WIDTH", MAV_PARAM_TYPE_INT16, &osd.boxes[1].w, &do_update_pthy),
	PARAM("BOX_2_HEIGHT", MAV_PARAM_TYPE_INT16, &osd.boxes[1].h, &do_update_pthy),
	PARAM("BOX_2_COLOR", MAV_PARAM_TYPE_INT8, &osd.boxes[1].color, &do_update_pthy),
	PARAM("BOX_2_MIX", MAV_PARAM_TYPE_INT8, &osd.boxes[1].mix, &do_update_pthy),

	PARAM("BOX_3_X", MAV_PARAM_TYPE_INT16, &osd.boxes[2].x, &do_update_pthy),
	PARAM("BOX_3_Y", MAV_PARAM_TYPE_INT16, &osd.boxes[2].y, &do_update_pthy),
	PARAM("BOX_3_WIDTH", MAV_PARAM_TYPE_INT16, &osd.boxes[2].w, &do_update_pthy),
	PARAM("BOX_3_HEIGHT", MAV_PARAM_TYPE_INT16, &osd.boxes[2].h, &do_update_pthy),
	PARAM("BOX_3_COLOR", MAV_PARAM_TYPE_INT8, &osd.boxes[2].color, &do_update_pthy),
	PARAM("BOX_3_MIX", MAV_PARAM_TYPE_INT8, &osd.boxes[2].mix, &do_update_pthy),

	PARAM("BOX_4_X", MAV_PARAM_TYPE_INT16, &osd.boxes[3].x, &do_update_pthy),
	PARAM("BOX_4_Y", MAV_PARAM_TYPE_INT16, &osd.boxes[3].y, &do_update_pthy),
	PARAM("BOX_4_WIDTH", MAV_PARAM_TYPE_INT16, &osd.boxes[3].w, &do_update_pthy),
	PARAM("BOX_4_HEIGHT", MAV_PARAM_TYPE_INT16, &osd.boxes[3].h, &do_update_pthy),
	PARAM("BOX_4_COLOR", MAV_PARAM_TYPE_INT8, &osd.boxes[3].color, &do_update_pthy),
	PARAM("BOX_4_MIX", MAV_PARAM_TYPE_INT8, &osd.boxes[3].mix, &do_update_pthy),

	PARAM("BOX_5_X", MAV_PARAM_TYPE_INT16, &osd.boxes[4].x, &do_update_pthy),
	PARAM("BOX_5_Y", MAV_PARAM_TYPE_INT16, &osd.boxes[4].y, &do_update_pthy),
	PARAM("BOX_5_WIDTH", MAV_PARAM_TYPE_INT16, &osd.boxes[4].w, &do_update_pthy),
	PARAM("BOX_5_HEIGHT", MAV_PARAM_TYPE_INT16, &osd.boxes[4].h, &do_update_pthy),
	PARAM("BOX_5_COLOR", MAV_PARAM_TYPE_INT8, &osd.boxes[4].color, &do_update_pthy),
	PARAM("BOX_5_MIX", MAV_PARAM_TYPE_INT8, &osd.boxes[4].mix, &do_update_pthy),

	PARAM("BOX_6_X", MAV_PARAM_TYPE_INT16, &osd.boxes[5].x, &do_update_pthy),
	PARAM("BOX_6_Y", MAV_PARAM_TYPE_INT16, &osd.boxes[5].y, &do_update_pthy),
	PARAM("BOX_6_WIDTH", MAV_PARAM_TYPE_INT16, &osd.boxes[5].w, &do_update_pthy),
	PARAM("BOX_6_HEIGHT", MAV_PARAM_TYPE_INT16, &osd.boxes[5].h, &do_update_pthy),
	PARAM("BOX_6_COLOR", MAV_PARAM_TYPE_INT8, &osd.boxes[5].color, &do_update_pthy),
	PARAM("BOX_6_MIX", MAV_PARAM_TYPE_INT8, &osd.boxes[5].mix, &do_update_pthy),

	PARAM("BOX_7_X", MAV_PARAM_TYPE_INT16, &osd.boxes[6].x, &do_update_pthy),
	PARAM("BOX_7_Y", MAV_PARAM_TYPE_INT16, &osd.boxes[6].y, &do_update_pthy),
	PARAM("BOX_7_WIDTH", MAV_PARAM_TYPE_INT16, &osd.boxes[6].w, &do_update_pthy),
	PARAM("BOX_7_HEIGHT", MAV_PARAM_TYPE_INT16, &osd.boxes[6].h, &do_update_pthy),
	PARAM("BOX_7_COLOR", MAV_PARAM_TYPE_INT8, &osd.boxes[6].color, &do_update_pthy),
	PARAM("BOX_7_MIX", MAV_PARAM_TYPE_INT8, &osd.boxes[6].mix, &do_update_pthy),
		
	PARAM("BOX_8_X", MAV_PARAM_TYPE_INT16, &osd.boxes[7].x, &do_update_pthy),
	PARAM("BOX_8_Y", MAV_PARAM_TYPE_INT16, &osd.boxes[7].y, &do_update_pthy),
	PARAM("BOX_8_WIDTH", MAV_PARAM_TYPE_INT16, &osd.boxes[7].w, &do_update_pthy),
	PARAM("BOX_8_HEIGHT", MAV_PARAM_TYPE_INT16, &osd.boxes[7].h, &do_update_pthy),
	PARAM("BOX_8_COLOR", MAV_PARAM_TYPE_INT8, &osd.boxes[7].color, &do_update_pthy),
	PARAM("BOX_8_MIX", MAV_PARAM_TYPE_INT8, &osd.boxes[7].mix, &do_update_pthy),

	PARAM("PT_IND_X", MAV_PARAM_TYPE_INT16, &osd.pt_widget.x, NULL), 
	PARAM("PT_IND_Y", MAV_PARAM_TYPE_INT16, &osd.pt_widget.y, NULL),

	PARAM("EKF_DET_X", MAV_PARAM_TYPE_INT16, &osd.ekf_detail.x, NULL), 
	PARAM("EKF_DET_Y", MAV_PARAM_TYPE_INT16, &osd.ekf_detail.y, NULL), 
	PARAM("EKF_DET_W", MAV_PARAM_TYPE_INT8, &osd.ekf_detail.w, NULL), 
	PARAM("EKF_DET_H", MAV_PARAM_TYPE_INT16, &osd.ekf_detail.h, NULL), 

	PARAM("VIBE_DET_X", MAV_PARAM_TYPE_INT16, &osd.vibe_detail.x, NULL),
	PARAM("VIBE_DET_Y", MAV_PARAM_TYPE_INT16, &osd.vibe_detail.y, NULL),
    PARAM("VIBE_DET_W", MAV_PARAM_TYPE_INT8, &osd.vibe_detail.w, NULL),
	PARAM("VIBE_DET_H", MAV_PARAM_TYPE_INT16, &osd.vibe_detail.h, NULL), 

	PARAM("RCOUT_X", MAV_PARAM_TYPE_INT16, &osd.rc_out.x, NULL),
	PARAM("RCOUT_Y", MAV_PARAM_TYPE_INT16, &osd.rc_out.y, NULL),
    PARAM("RCOUT_CHNUM", MAV_PARAM_TYPE_INT8, &osd.rc_out.chnum, NULL),


	PARAM("TEST_PIP_PAGE",MAV_PARAM_TYPE_UINT8, &g.pip_page, &update_pip),
	PARAM("TEST_OSD_PAGE", MAV_PARAM_TYPE_UINT8, &g.visible_osd_page, &do_update_pthy),

    PARAM("WRITE_SETTINGS",MAV_PARAM_TYPE_UINT8, &g.write_settings, &do_settings_save),


	PARAM("DEBUG_LOOPTIME", MAV_PARAM_TYPE_UINT8, &g.debug_looptime,NULL),

	PARAM_END
};


void do_update_pthy()
{
	//initiate redraw of boxes on pthy page
	g.pthy_redraw = true;
	OSD256_clear_screen(PTH_Y, 0); //And clean the pthy display
}

void do_settings_save()
{
	g.write_settings = 0;
	save_settings();
	message_buffer_add_line(STR_SETTINGS_SAVED, 4);

}

void update_pip()
{
	for (uint8_t i = 1; i<5; i++)
	{
		tw_ch_set_input(i, osd.video_channels[g.pip_page][i].input);
	
		tw_ch_settings(i, osd.video_channels[g.pip_page][i].enable,
			osd.video_channels[g.pip_page][i].popup);
	
		tw_ch_set_window(i, osd.video_channels[g.pip_page][i].pos_h,
			osd.video_channels[g.pip_page][i].pos_v,
			osd.video_channels[g.pip_page][i].len_h);
    
	}

}


void update_vout_settings()
{
	uint8_t reg1ab = 0;
	if (osd.color_bar_x) reg1ab =  reg1ab | 0x08;
	if (osd.color_kill_x) reg1ab = reg1ab | 0x04;
	tw_write_register(0x1ab, reg1ab);

	if (osd.vout1_gain > 7) osd.vout1_gain = 7;
	if (osd.vout2_gain > 7) osd.vout2_gain = 7;
	if (osd.vout3_gain > 7) osd.vout3_gain = 7;
	
	uint8_t reg041 = 0;
	reg041 = (osd.vout2_gain << 4) + osd.vout1_gain;
	tw_write_register(0x041, reg041);
	tw_write_register(0x042, osd.vout3_gain);



}


void update_vin_settings()
{
	//Check some boundaries and update all four channels
	for (int i = 0; i < 4; i++)
	{
		if (osd.vin_params[i].sharpening > 0x0f) osd.vin_params[i].sharpening = 0x0f;
		if (osd.vin_params[i].peaking > 0x07) osd.vin_params[i].peaking = 0x07;

		tw_write_register(i * 0x10 + 0x08, 0x30 + osd.vin_params[i].sharpening);
		tw_write_register(i * 0x10 + 0x09, osd.vin_params[i].contrast);
		tw_write_register(i * 0x10 + 0x0a, osd.vin_params[i].brightness);
		tw_write_register(i * 0x10 + 0x0b, osd.vin_params[i].saturation);
		tw_write_register(i * 0x10 + 0x0c, osd.vin_params[i].saturation);
		tw_write_register(i * 0x10 + 0x01, osd.vin_params[i].peaking);

		char func_reg = 0;
		if (osd.vin_params[i].enhance) func_reg += BIT3;
		if (osd.vin_params[i].h_mirror) func_reg += BIT5;
		if (osd.vin_params[i].v_mirror) func_reg += BIT4;
		if (osd.vin_params[i].boundary) func_reg += BIT1;
		tw_write_register(0x111 + (i * 0x08), func_reg);
	}





}

/*
void update_channel_onoff()
{
	osd.ctr_saved_state[1] = 5;
	debug("Called\n");

}
*/
const char *mavdata_type_name[] = {
	"CHAR", "UINT8_T", "INT8_T",
	"UINT16_T", "INT16_T",
	"UINT32_T", "INT32_T",
	"UINT64_T", "INT64_T",
	"FLOAT", "DOUBLE"
};


void get_parameter_count()
{
	total_params = 0;

	while (parameters[total_params].name[0] != '\0')
	{
		total_params++;

	}
}


unsigned int get_parameter_index(char *name)
{
	int idx;

	if (total_params == 0) get_parameter_count();

	for (idx = 0; idx < total_params; idx++) {
		if (strcmp(name, parameters[idx].name) == 0)
			break;
	}
	return idx;
}

float get_parameter_value(int idx, char *name)
{
//	struct param_def p;
//	struct param_value pv;

//	p.value = &pv;

	if (total_params == 0) get_parameter_count();

	if (idx == -1)
		idx = get_parameter_index(name);

	if (idx < total_params) {
		strcpy(name, parameters[idx].name);
		return cast2float(parameters[idx].value, parameters[idx].type);
	}
	else
	{
		return 0;
	}
}

int params_set_value(char *name, float value, uint8_t trigger_cbk)
{
	struct param_def *p;
	int idx;

	idx = get_parameter_index(name);
	//debug("name='%s' idx=%d\n", name, idx);
	if (idx < total_params) {
		p = &parameters[idx];
		cast2param(p, value);
		if ((p->cbk != NULL) && trigger_cbk)
			p->cbk();
	}
	return idx;
}




float cast2float(void *value, uint8_t type)
{
	switch (type) {
	case MAV_PARAM_TYPE_UINT8:
		return (float) *((uint8_t*)(value));
	case MAV_PARAM_TYPE_INT8:
		return (float) *((char*)(value));
	case MAV_PARAM_TYPE_UINT16:
		return (float) *((uint16_t*)(value));
	case MAV_PARAM_TYPE_INT16:
		return (float) *((short*)(value));
	case MAV_PARAM_TYPE_REAL32:
		return (float) *((float*)(value));
	default:
		return 0;
	}
}

void cast2param(struct param_def *p, float v)
{
	switch (p->type) {
	case MAV_PARAM_TYPE_UINT8:
		*((uint8_t*)(p->value)) = (uint8_t)v;
		break;
	case MAV_PARAM_TYPE_INT8:
		*((char*)(p->value)) = (char)v;
		break;
	case MAV_PARAM_TYPE_UINT16:
		*((uint16_t*)(p->value)) = (uint16_t)v;
		break;
	case MAV_PARAM_TYPE_INT16:
		*((short*)(p->value)) = (short)v;
		break;
	case MAV_PARAM_TYPE_REAL32:
		*((float*)(p->value)) = (float)v;
		break;
	default:
		break;
	}
}
