EosBandi/OSDeluxe/tw_font.h

/*
    OSDeluxe - Color PIP Mavlink OSD
    Copyright (C) 2018  Andras Schaffer - Dronedoktor.eu

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
    With Grateful Acknowledgements to the projects:
        AlceOSD by Luis Alves
        PlayUAV OSD
        Brain FPV Flight Controller(https://github.com/BrainFPV/TauLabs) by Tau Labs

 */



#define FONT0_X 16
#define FONT0_Y 20


const uint8_t ufont_16x20[] = {
	0x00, 0x00, 0x00, 0x00,
	0x00, 0x00, 0x00, 0x00,
	0x00, 0x00, 0x00, 0x00,
	0x00, 0x00, 0x00, 0x00,
	0x00, 0x00, 0x00, 0x00,
	0x00, 0x00, 0x00, 0x00,
	0x00, 0x00, 0x00, 0x00,
	0x00, 0x00, 0x00, 0x00,
	0x00, 0x00, 0x00, 0x00,
	0x00, 0x00, 0x00, 0x00,
	0x00, 0x00, 0x00, 0x00,
	0x00, 0x00, 0x00, 0x00,
	0x00, 0x00, 0x00, 0x00,
	0x00, 0x00, 0x00, 0x00,
	0x00, 0x00, 0x00, 0x00,
	0x00, 0x00, 0x00, 0x00,
	0x00, 0x00, 0x00, 0x00,
	0x00, 0x00, 0x00, 0x00,
	0x00, 0x00, 0x00, 0x00,
	0x00, 0x00, 0x00, 0x00,

	0x00, 0x05, 0x50, 0x00,
	0x00, 0x17, 0xd4, 0x00,
	0x00, 0x1f, 0xf4, 0x00,
	0x00, 0x1f, 0xf4, 0x00,
	0x00, 0x1f, 0xf4, 0x00,
	0x00, 0x1f, 0xf4, 0x00,
	0x00, 0x1f, 0xf4, 0x00,
	0x00, 0x1f, 0xf4, 0x00,
	0x00, 0x17, 0xd4, 0x00,
	0x00, 0x07, 0xd0, 0x00,
	0x00, 0x07, 0xd0, 0x00,
	0x00, 0x05, 0x50, 0x00,
	0x00, 0x05, 0x50, 0x00,
	0x00, 0x07, 0xd0, 0x00,
	0x00, 0x07, 0xd0, 0x00,
	0x00, 0x05, 0x50, 0x00,
	0x00, 0x00, 0x00, 0x00,
	0x00, 0x00, 0x00, 0x00,
	0x00, 0x00, 0x00, 0x00,
	0x00, 0x00, 0x00, 0x00,

	0x00, 0x00, 0x00, 0x00,
	0x00, 0x00, 0x00, 0x00,
	0x15, 0x40, 0x00, 0x00,
	0x1f, 0x50, 0x00, 0x00,
	0x1f, 0xd4, 0x00, 0x00,
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
	0x11, 0x33, 0x33, 0x33, 0x33, 0x33, 0x31, 0x10,
	0x01, 0x13, 0x33, 0x33, 0x33, 0x33, 0x11, 0x00,
	0x01, 0x13, 0x33, 0x33, 0x33, 0x33, 0x11, 0x00,
	0x00, 0x11, 0x13, 0x33, 0x33, 0x11, 0x10, 0x00,
	0x00, 0x01, 0x11, 0x11, 0x11, 0x11, 0x00, 0x00,
	0x00, 0x00, 0x01, 0x11, 0x11, 0x00, 0x00, 0x00
};
