EosBandi/OSDeluxe/globals.h

/*
OSDeluxe - Color PIP Mavlink OSD
Copyright (C) 2018  Andras Schaffer - Dronedoktor.eu

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
With Grateful Acknowledgements to the projects:
AlceOSD by Luis Alves
PlayUAV OSD
Brain FPV Flight Controller(https://github.com/BrainFPV/TauLabs) by Tau Labs

*/

#ifndef _GLOBALS_H_
#define _GLOBALS_H_

#define EEPROM_VERSION 0x10

#define MESSAGE_BUFFER_LINES 20
#define NO_HEADING 0xfff


//Globally used variables are put into a struct for referencing

struct global_variables_t
{

    unsigned char mav_type;  // MAV type from mavlink heartbeat;
    unsigned char base_mode; // It comes from the arming...
    int heading;
    float airspeed;
    float groundspeed;
    int throttle;
    bool arming_status;
    home_data_t home;
    int launch_heading;

    unsigned int mode;

    float altitude;
    float vario;

    float variot;

    short vario_graph[80];
    unsigned char vgraph_idx;

    int ekfvel;
    int ekfposh;
    int ekfposv;
    int ekfcompass;
    int ekfterrain;

	int vibex;
    int vibey;
    int vibez;

	uint32_t clip0;
    uint32_t clip1;
    uint32_t clip2;

    float vx;               // X speed in m/s
    float vy;               // Y speed in m/s
    float yaw;              // Yaw in rad
    float cos_yaw, sin_yaw; // Precalculated yaw sin/cos values

	int pitch;
    int roll;


    unsigned short wp_seq;
    unsigned short wp_distance;
    short wp_target_bearing;

    unsigned char rssi;
    unsigned char remote_rssi;


    int b1_power; // Battery 1 Power (Watts)
    float b1_current;
    float b1_voltage;
    unsigned char b1_remaining_capacity;

    int b2_power; // Battery 1 Power (Watts)
    float b2_current;
    float b2_voltage;

    unsigned char ctr_state[4];
    unsigned char ctr_saved_state[4];

    unsigned char visible_osd_page; // The OSD page to show. (bit coded)
    unsigned char pip_page;

    unsigned int rcin[17];
    unsigned int rc_rssi;

	uint16_t rcout[9];

    char system_status; // Se MAVLINK_STATE enum

    char message_buffer[MESSAGE_BUFFER_LINES][52]; // 20 line of 52 character message_buffer
    uint8_t message_severity[MESSAGE_BUFFER_LINES];
    uint8_t message_buffer_line;
    uint8_t message_buffer_display_line;
    long message_buffer_display_time;
    bool message_display; // we have message to display in the buffer
    bool clear_req;

    char message_archive[MESSAGE_BUFFER_LINES][52];
    char message_archive_severity[MESSAGE_BUFFER_LINES];
    uint8_t message_archive_line = 0;

    bool displayed_arming_status;
    unsigned long armed_start_time;

    int displayed_mode;

    unsigned long last_capacity_query;
    unsigned long last_outgoing_heartbeat;

    char test_byte;

    uint8_t write_settings;
    uint8_t debug_looptime;

    bool pthy_redraw; // indicated that we need to redraw osd content on y path.
    bool powerup; // Are we resetting or powering up from zero.

	uint8_t detected_cell_count;
};

extern global_variables_t g;

#endif
