EosBandi/OSDeluxe/home_calc.cpp

/*
    OSDeluxe - Color PIP Mavlink OSD
    Copyright (C) 2018  Andras Schaffer - Dronedoktor.eu

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
    With Grateful Acknowledgements to the projects:
        AlceOSD by Luis Alves
        PlayUAV OSD
        Brain FPV Flight Controller(https://github.com/BrainFPV/TauLabs) by Tau Labs

 */

#include "osdeluxe.h"

void init_home(void)
{
    g.home.lock = HOME_NONE;
    g.home.last_calc = millis();
}

void calc_home(void)
{
    mavlink_message_t this_msg;

    switch (g.home.lock)
    {
    case HOME_NONE:
    default:
        if (mavdata_age(MAVLINK_MSG_ID_HEARTBEAT) > 5000) return;
        /* check arming status */
        if (g.base_mode & MAV_MODE_FLAG_SAFETY_ARMED) g.home.lock = HOME_WAIT;
        break;
    case HOME_WAIT:
        if (mavdata_age(MAVLINK_MSG_ID_MISSION_ITEM) > 2000)
        {
            /* when UAV is armed, home is WP0 */
            mavlink_msg_mission_request_pack(OSD_SYS_ID, MAV_COMP_ID_OSD, &this_msg, 0, MAV_COMP_ID_ALL,0,0);
            mavlink_send_msg(&this_msg);
        }
        else
        {
            g.home.lock = HOME_GOT;
        }
        break;
    case HOME_GOT:
        g.home.lock = HOME_LOCKED;
        break;
    case HOME_LOCKED:
    {
        // Do nothing, this calculated at the MAVLINK_MSG_ID_GLOBAL_POSITION_INT message parsing in mavlink.cpp
        break;
    }
    }
}

float earth_distance(struct gps_coord_t *c1, struct gps_coord_t *c2)
{
    float dphi, dlam, sin_dphi, sin_dlam;
    float a, c;

    dphi = c2->lat - c1->lat;
    dlam = c2->lon - c1->lon;
    sin_dphi = sin(dphi/2);
    sin_dlam = sin(dlam/2);
    a = sin_dphi * sin_dphi + cos(c1->lat) * cos(c2->lat) * sin_dlam * sin_dlam;
    c = 2 * atan2(sqrt(a), sqrt(1-a));
    c = c * ((float) EARTH_RADIUS);

    return c;
}

float get_bearing(struct gps_coord_t *c1, struct gps_coord_t *c2)
{
    float y = sin(c2->lon - c1->lon) * cos(c2->lat);
    float x = cos(c1->lat)*sin(c2->lat) - sin(c1->lat)*cos(c2->lat)*cos(c2->lon - c1->lon);
    return RAD2DEG(atan2(y, x));
}


void find_launch_heading()
{
	if (g.home.lock != HOME_LOCKED)
		return;

	if (g.launch_heading != NO_HEADING)
		return;

	if ((g.throttle > 10) && (g.airspeed > 5) && (g.altitude > 5))
	{
		g.launch_heading = g.heading;
		message_buffer_add_line(STR_LAUNCH_DIRECTION_OK , 4);

	}


}
